AlexanderSaal/Analog_Computer_4-Quadrant_Division_Module/Analog_Computer_Division_Module/schematic/PCB-1.png

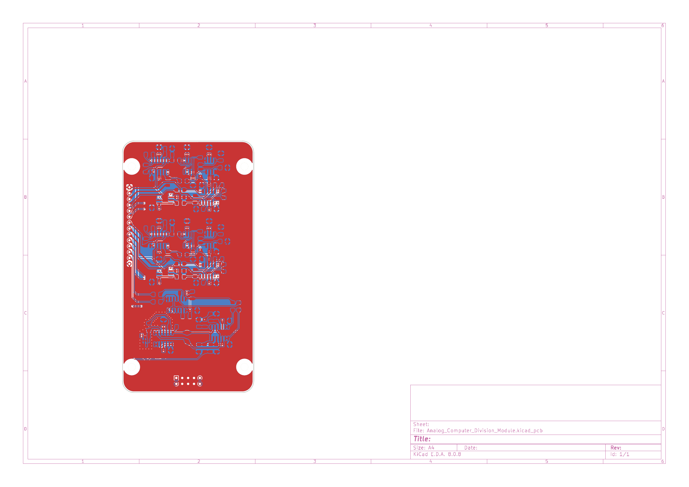
Analog_Computer_Division_Module/schematic/PCB-1.png
